ColdFrontWI/Hornet_Cockpit/DXF Files/Panel/Bitmap/Readme.md

# Panel bitmaps

One of the main references when was drawing the panel was the NATOPS instrument panel foldout.  The .png files here
are literal screengrabs from the PDF that I inserted into QCAD and used as a reference for switch spacing.
