ColdFrontWI/Hornet_Cockpit/DXF Files/Panel/Bitmap/AMPCD Full.png

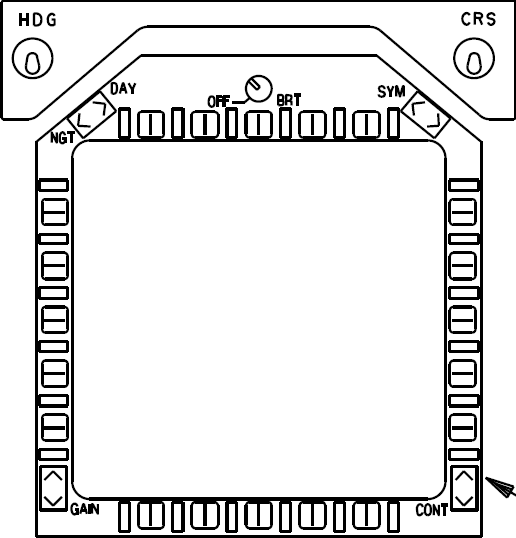
DXF Files/Panel/Bitmap/AMPCD Full.png
