ColdFrontWI/Hornet_Cockpit/DXF Files/Panel/Bitmap/AMPCD Top.png

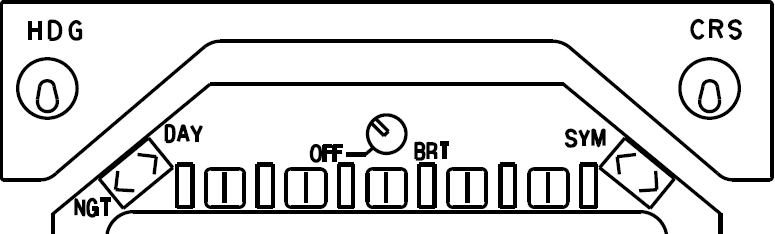
DXF Files/Panel/Bitmap/AMPCD Top.png
