ColdFrontWI/Hornet_Cockpit/DXF Files/Panel/Bitmap/Cons Left Ext Lt.PNG

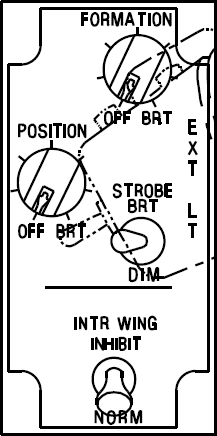
DXF Files/Panel/Bitmap/Cons Left Ext Lt.PNG
