ColdFrontWI/Hornet_Cockpit/DXF Files/Panel/Bitmap/Cons Left Fuel FCS.PNG

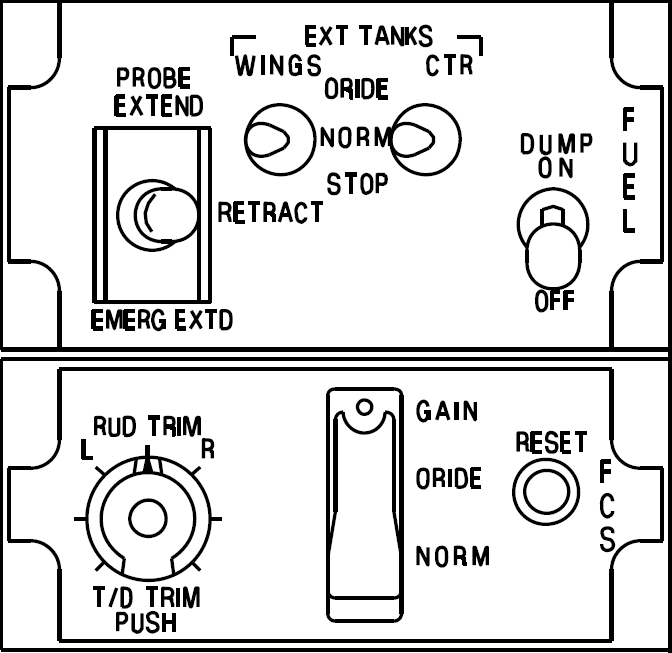
DXF Files/Panel/Bitmap/Cons Left Fuel FCS.PNG
