ColdFrontWI/Hornet_Cockpit/DXF Files/Panel/Bitmap/Cons Left IFF.PNG

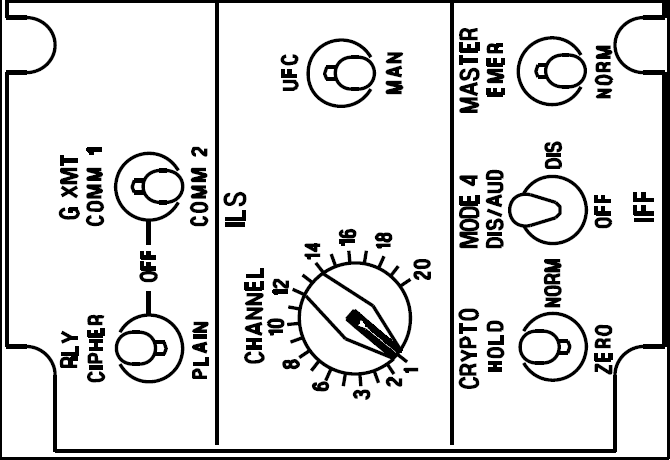
DXF Files/Panel/Bitmap/Cons Left IFF.PNG
