ColdFrontWI/Hornet_Cockpit/DXF Files/Panel/Bitmap/Cons Left OBOGS.PNG

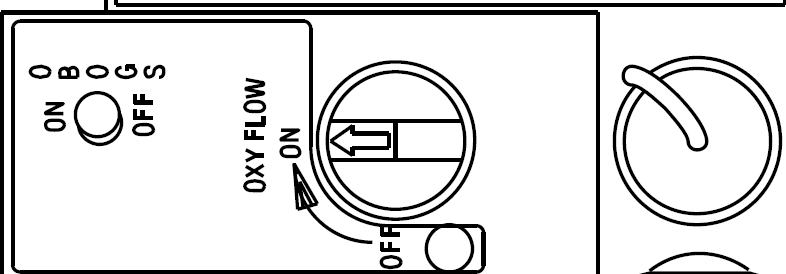
DXF Files/Panel/Bitmap/Cons Left OBOGS.PNG
