ColdFrontWI/Hornet_Cockpit/DXF Files/Panel/Bitmap/Cons Left Vol.PNG

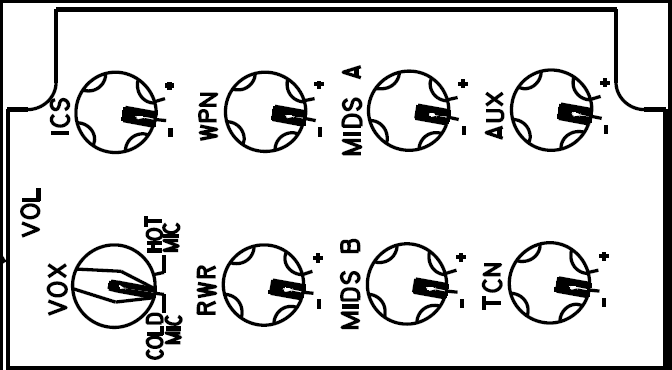
DXF Files/Panel/Bitmap/Cons Left Vol.PNG
