ColdFrontWI/Hornet_Cockpit/DXF Files/Panel/Bitmap/Cons Right Elec.PNG

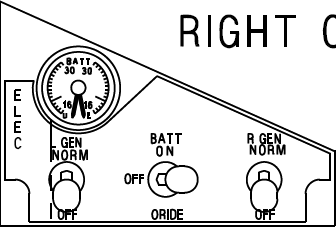
DXF Files/Panel/Bitmap/Cons Right Elec.PNG
