ColdFrontWI/Hornet_Cockpit/DXF Files/Panel/Bitmap/Cons Right ESC.PNG

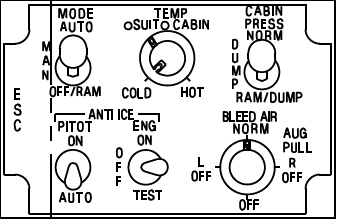
DXF Files/Panel/Bitmap/Cons Right ESC.PNG
