ColdFrontWI/Hornet_Cockpit/DXF Files/Panel/Bitmap/Cons Right Front.PNG

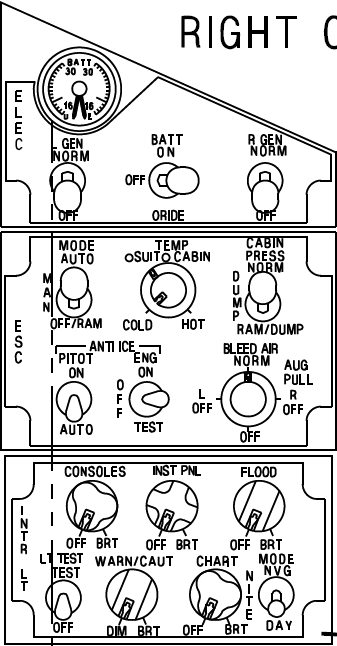
DXF Files/Panel/Bitmap/Cons Right Front.PNG
