ColdFrontWI/Hornet_Cockpit/DXF Files/Panel/Bitmap/Cons Right Int Light.PNG

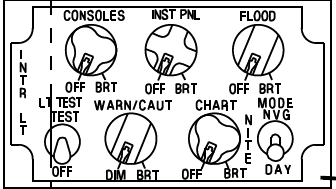
DXF Files/Panel/Bitmap/Cons Right Int Light.PNG
