ColdFrontWI/Hornet_Cockpit/DXF Files/Panel/Bitmap/Cons Right Sensor.PNG

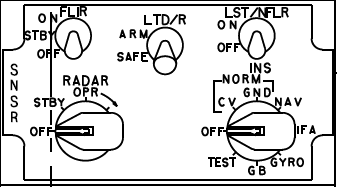
DXF Files/Panel/Bitmap/Cons Right Sensor.PNG
