ColdFrontWI/Hornet_Cockpit/DXF Files/Panel/Bitmap/Flight Inst.PNG

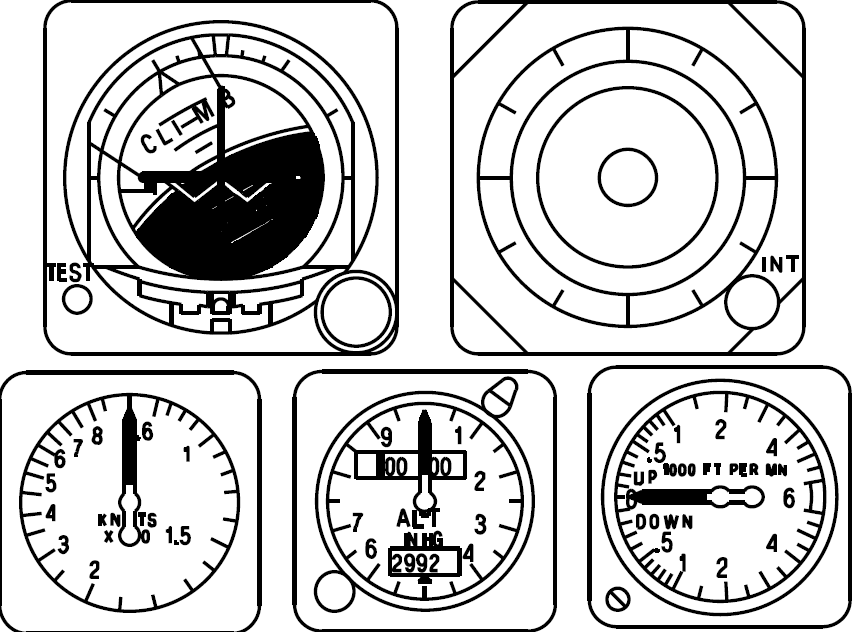
DXF Files/Panel/Bitmap/Flight Inst.PNG
