ColdFrontWI/Hornet_Cockpit/DXF Files/Panel/Bitmap/HMD, Spin Recovery.PNG

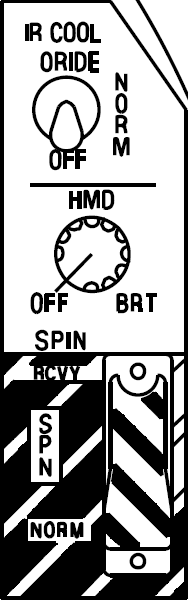
DXF Files/Panel/Bitmap/HMD, Spin Recovery.PNG
