ColdFrontWI/Hornet_Cockpit/DXF Files/Panel/Bitmap/HUD.png

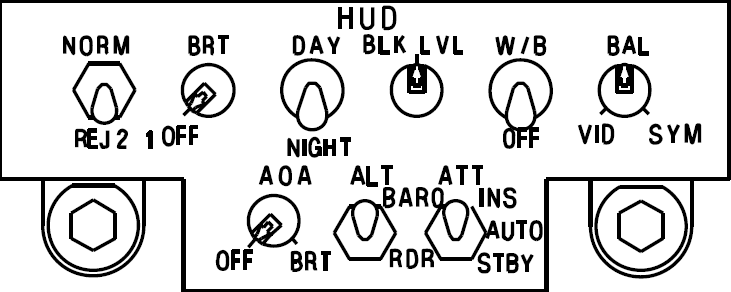
DXF Files/Panel/Bitmap/HUD.png
