ColdFrontWI/Hornet_Cockpit/DXF Files/Panel/Bitmap/Jett Select.PNG

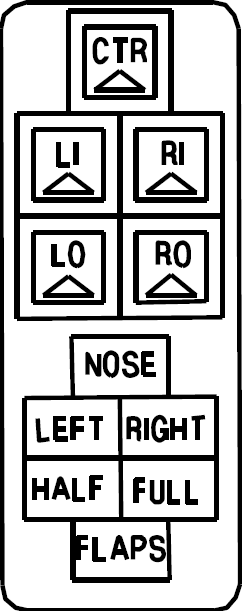
DXF Files/Panel/Bitmap/Jett Select.PNG
