ColdFrontWI/Hornet_Cockpit/DXF Files/Panel/Bitmap/Left Cons APU.PNG

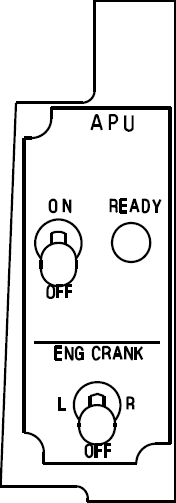
DXF Files/Panel/Bitmap/Left Cons APU.PNG
