ColdFrontWI/Hornet_Cockpit/DXF Files/Panel/Bitmap/Left Cons GndPwr Fire.PNG

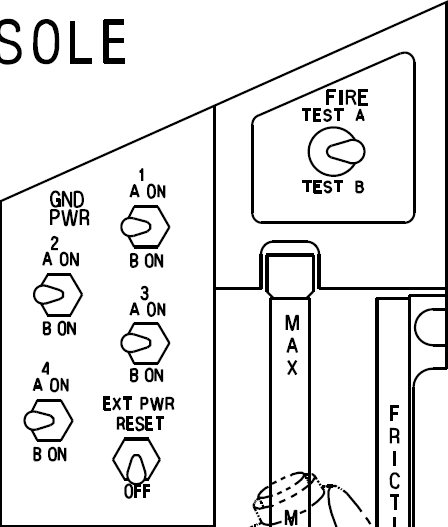
DXF Files/Panel/Bitmap/Left Cons GndPwr Fire.PNG
