ColdFrontWI/Hornet_Cockpit/DXF Files/Panel/Bitmap/Left Mech.PNG

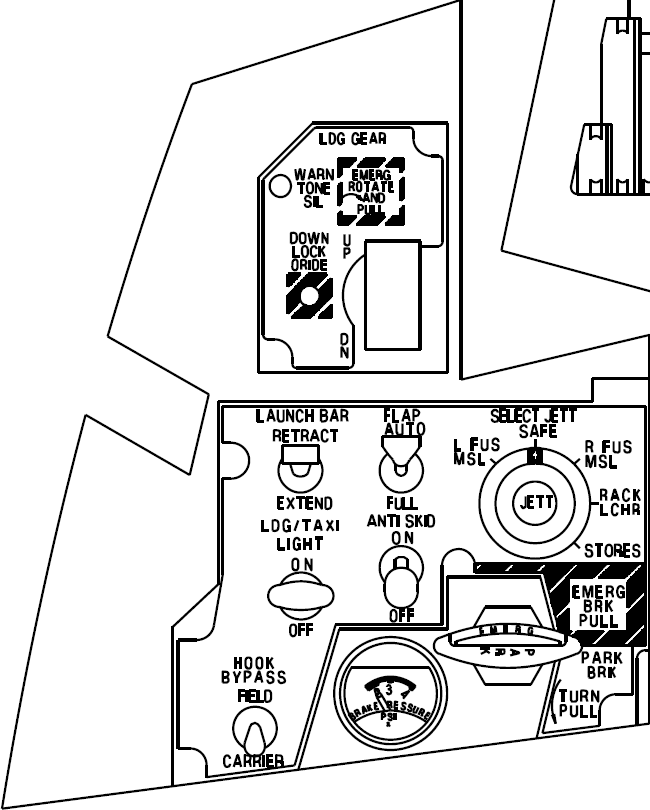
DXF Files/Panel/Bitmap/Left Mech.PNG
