ColdFrontWI/Hornet_Cockpit/DXF Files/Panel/Bitmap/Master Arm.PNG

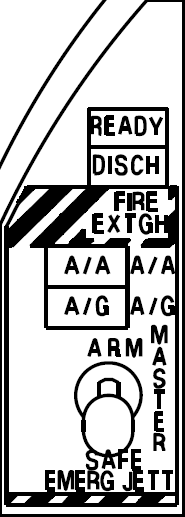
DXF Files/Panel/Bitmap/Master Arm.PNG
