ColdFrontWI/Hornet_Cockpit/DXF Files/Panel/Bitmap/Right Mech.PNG

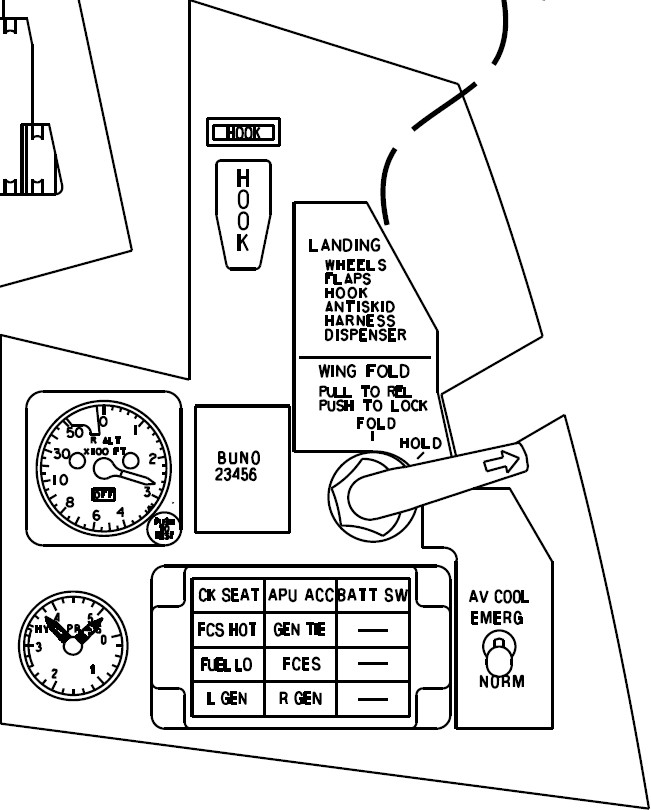
DXF Files/Panel/Bitmap/Right Mech.PNG
