ColdFrontWI/Hornet_Cockpit/DXF Files/Panel/Bitmap/TM Cougar MFD - crop.jpg

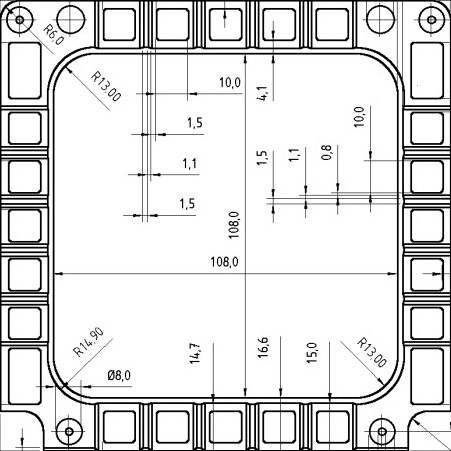
DXF Files/Panel/Bitmap/TM Cougar MFD - crop.jpg
