ColdFrontWI/Hornet_Cockpit/DXF Files/Panel/Bitmap/UFC.png

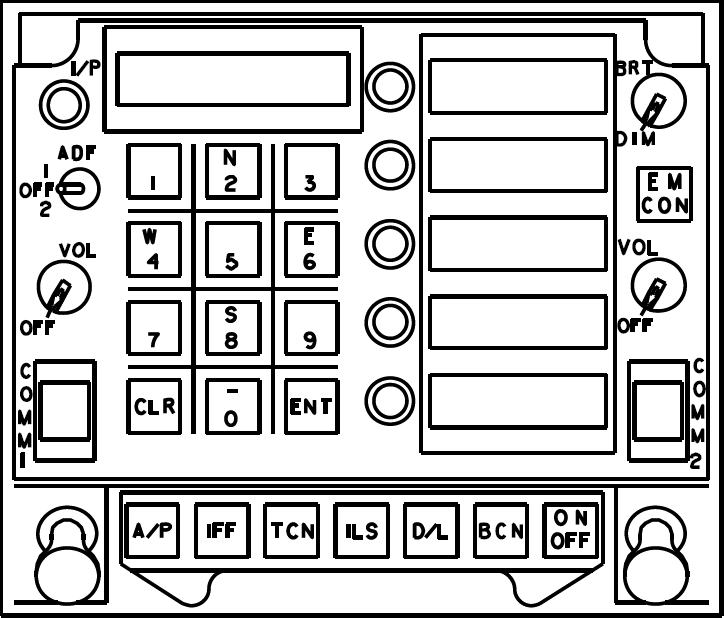
DXF Files/Panel/Bitmap/UFC.png
