ColdFrontWI/Hornet_Cockpit/Pictures/2020-05/IMG_7479.JPG

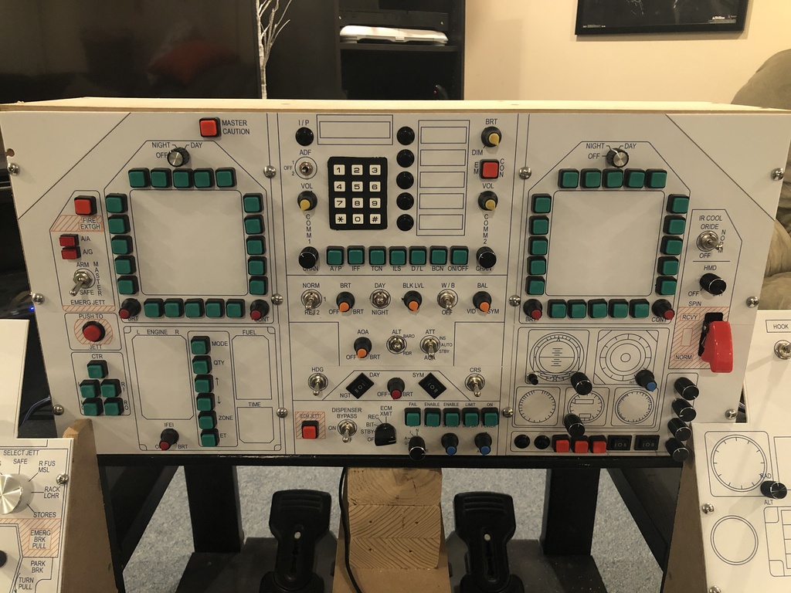
Pictures/2020-05/IMG_7479.JPG
