ColdFrontWI/Hornet_Cockpit/STL Files/Warthog-Virpil extensions/Pictures/IMG_7719.JPG

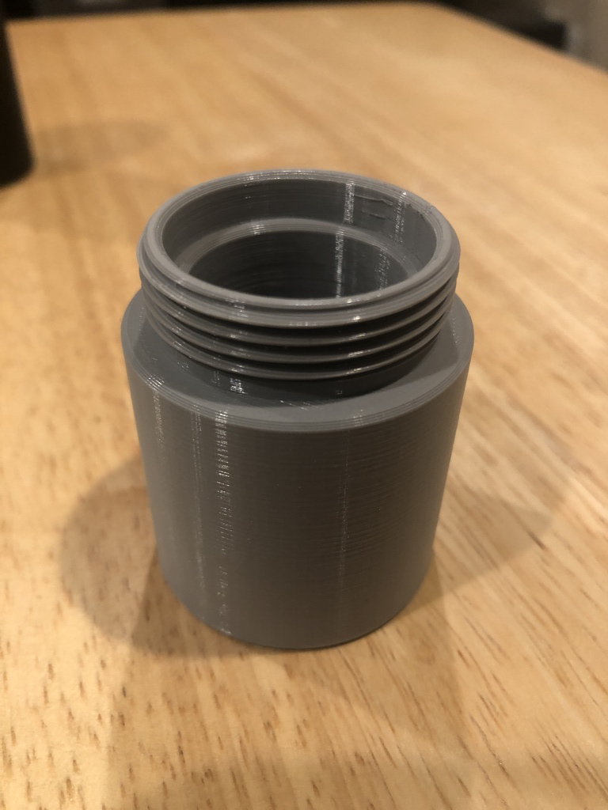
STL Files/Warthog-Virpil extensions/Pictures/IMG_7719.JPG
