ColdFrontWI/Hornet_Cockpit/STL Files/Warthog-Virpil extensions/Pictures/IMG_7722.JPG

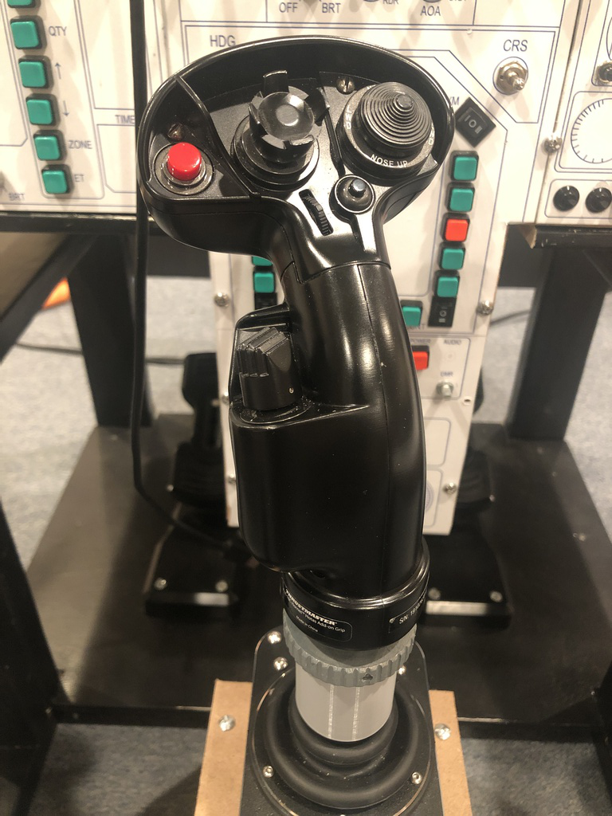
STL Files/Warthog-Virpil extensions/Pictures/IMG_7722.JPG
