ColdFrontWI/Hornet_Cockpit/STL Files/Knobs/Small volume knob.stl

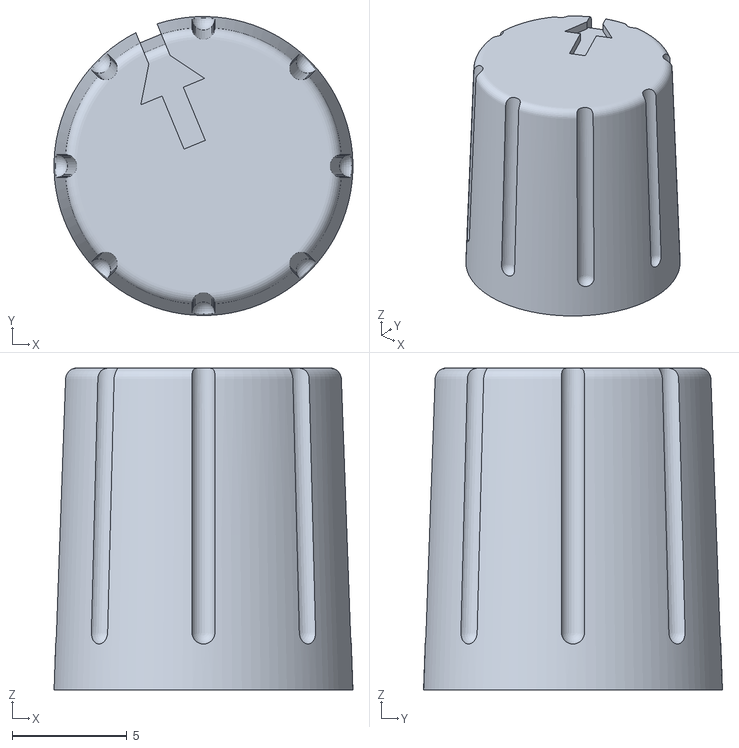
[picture p114: CAD file, 2020-09-19]
STL Files/Knobs/Small volume knob.stl
13.0 x 13.0 x 14.0
