ColdFrontWI/Hornet_Cockpit/STL Files/Other/Hand brake base.stl

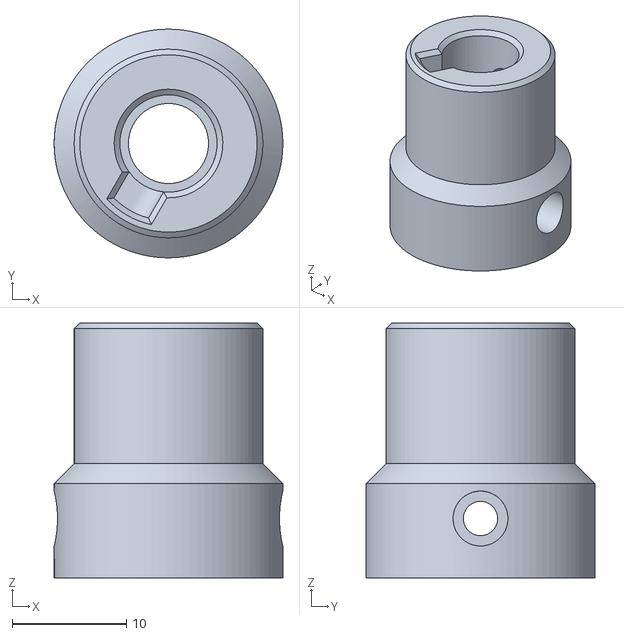
[picture p115: CAD file, 2020-09-13]
STL Files/Other/Hand brake base.stl
20.0 x 20.0 x 22.3
