ColdFrontWI/Hornet_Cockpit/STL Files/Switches/Sw - Landing & taxi lights.stl

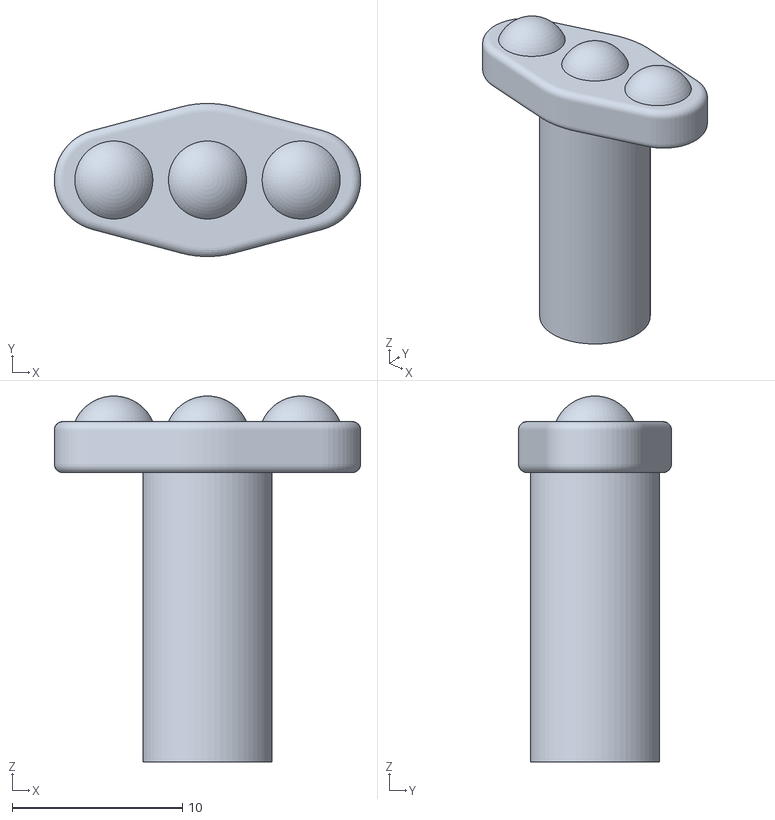
[picture p116: CAD file, 2020-08-24]
STL Files/Switches/Sw - Landing & taxi lights.stl
18.0 x 8.99 x 21.5
