ColdFrontWI/Hornet_Cockpit/STL Files/Warthog-Virpil extensions/WH ext 100mm, 36.5.stl

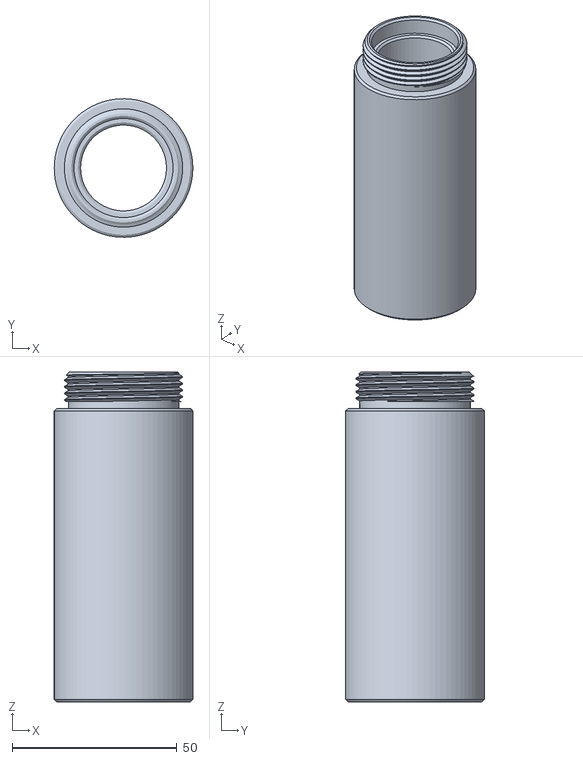
[picture p117: CAD file, 2020-09-23]
STL Files/Warthog-Virpil extensions/WH ext 100mm, 36.5.stl
42.0 x 42.0 x 100.0
