ColdFrontWI/Hornet_Cockpit/STL Files/Knobs/Smaller volume knob.stl

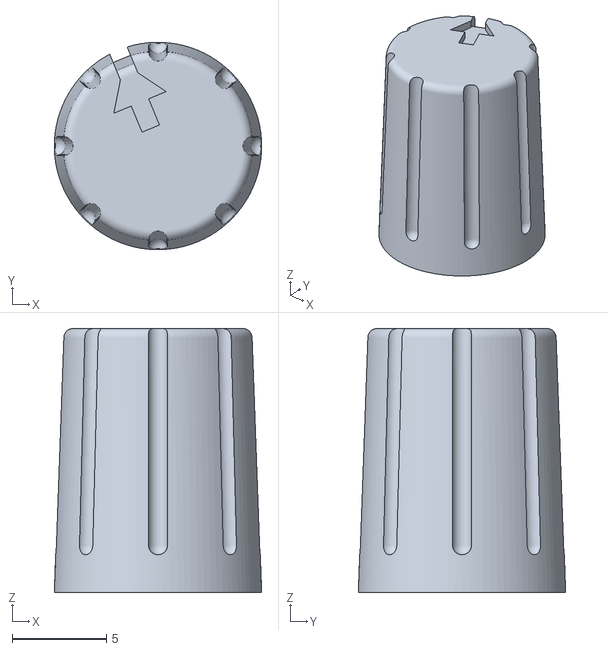
[picture p118: CAD file, 2020-09-19]
STL Files/Knobs/Smaller volume knob.stl
11.0 x 11.0 x 14.0
