ColdFrontWI/Hornet_Cockpit/STL Files/Other/Hand brake shaft.stl

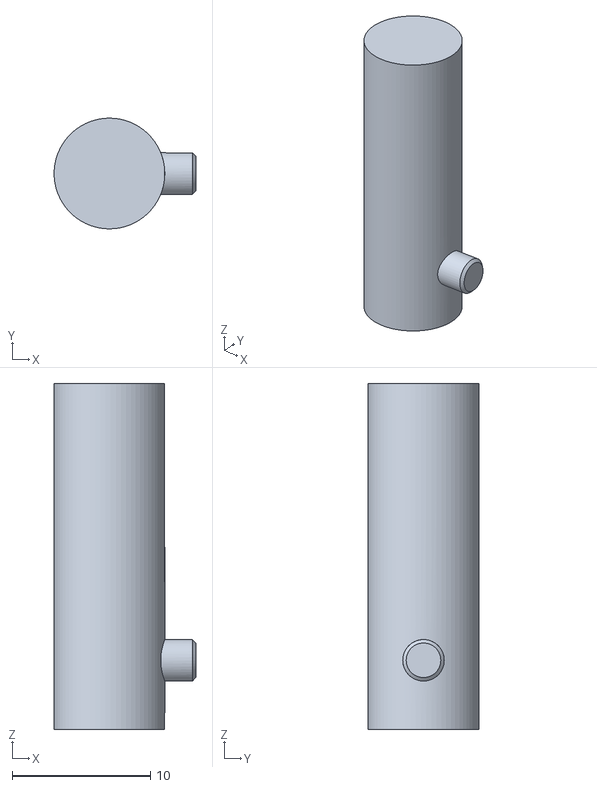
[picture p119: CAD file, 2020-09-13]
STL Files/Other/Hand brake shaft.stl
10.2 x 8.00 x 25.0
