ColdFrontWI/Hornet_Cockpit/STL Files/Switches/Sw - Flat.stl

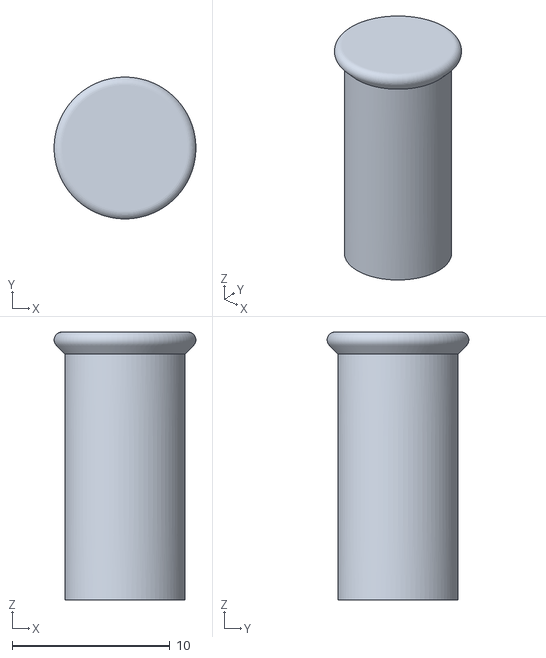
[picture p120: CAD file, 2020-08-24]
STL Files/Switches/Sw - Flat.stl
9.00 x 8.99 x 17.0
