ColdFrontWI/Hornet_Cockpit/STL Files/Knobs/Knob - Large pointy.stl

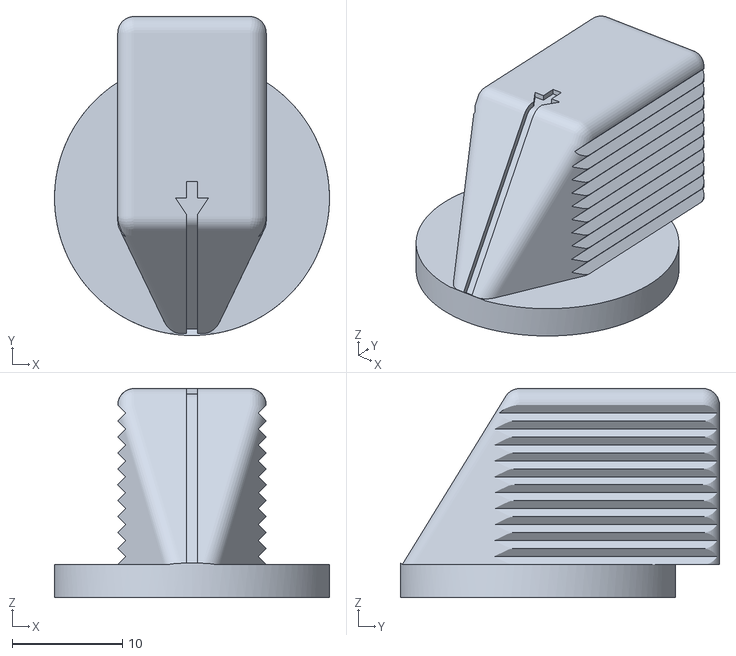
[picture p121: CAD file, 2020-09-13]
STL Files/Knobs/Knob - Large pointy.stl
25.0 x 29.0 x 19.0
