ColdFrontWI/Hornet_Cockpit/STL Files/Other/Dispense button.stl

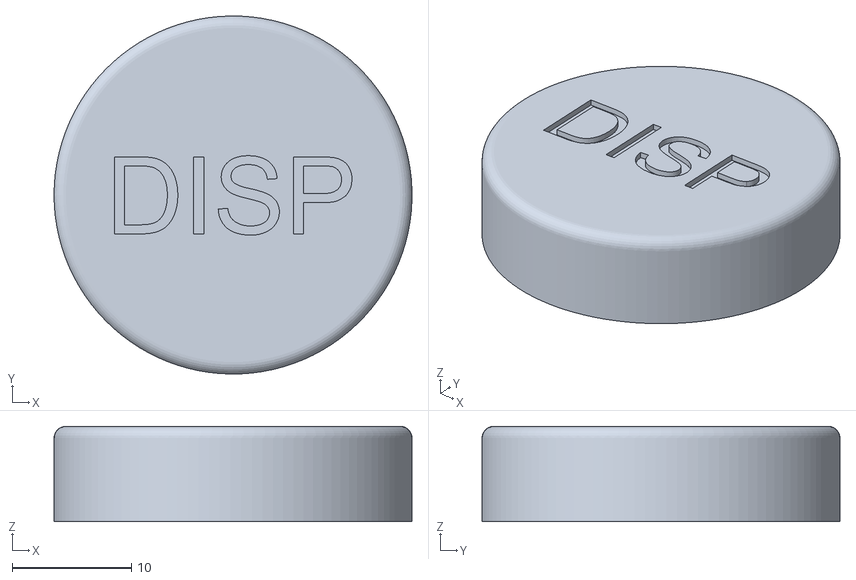
[picture p122: CAD file, 2020-09-13]
STL Files/Other/Dispense button.stl
30.0 x 30.0 x 8.00
