ColdFrontWI/Hornet_Cockpit/STL Files/Switches/Sw - Gear.stl

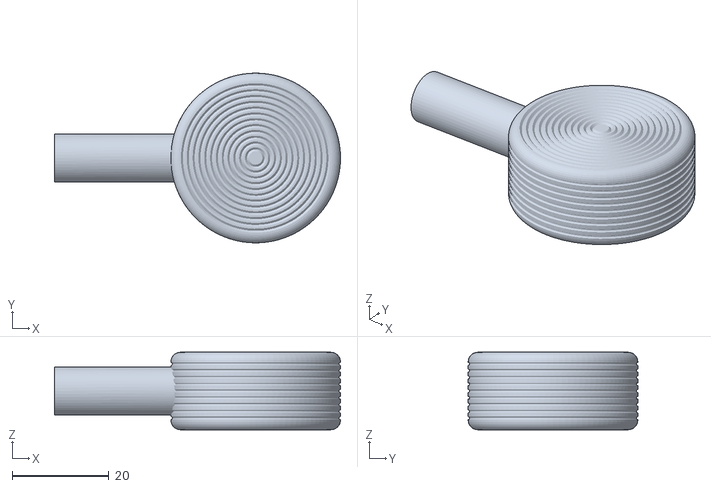
[picture p123: CAD file, 2020-08-24]
STL Files/Switches/Sw - Gear.stl
59.0 x 35.0 x 16.0
