ColdFrontWI/Hornet_Cockpit/STL Files/Knobs/Knob - Bleed air.stl

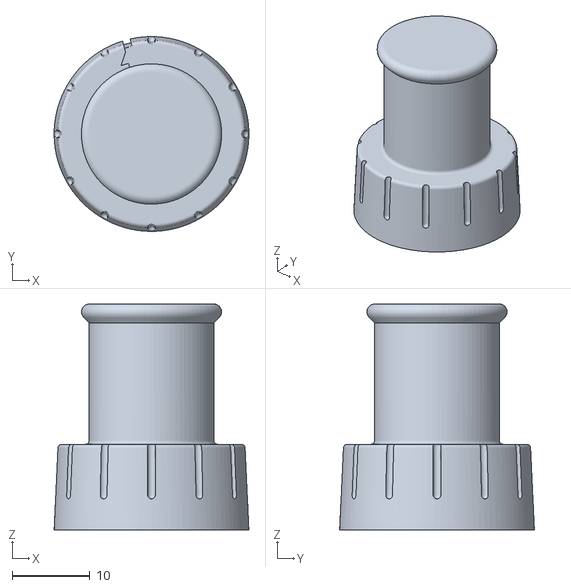
[picture p124: CAD file, 2020-09-05]
STL Files/Knobs/Knob - Bleed air.stl
25.0 x 25.0 x 29.0
