ColdFrontWI/Hornet_Cockpit/STL Files/Other/Hand brake top.stl

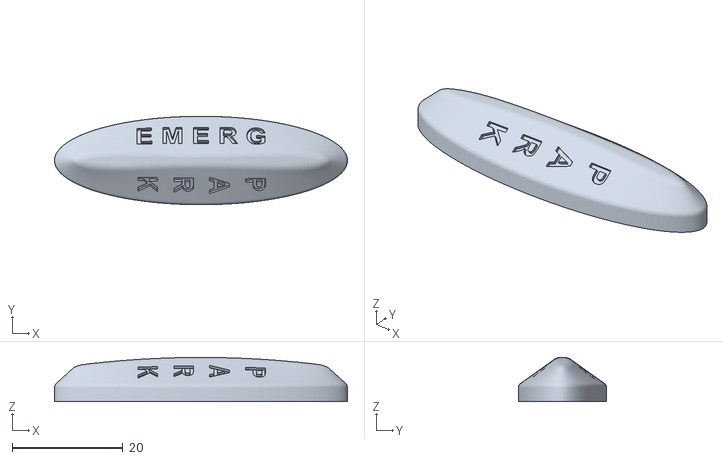
[picture p125: CAD file, 2020-09-13]
STL Files/Other/Hand brake top.stl
53.0 x 16.0 x 8.00
