ColdFrontWI/Hornet_Cockpit/STL Files/Switches/Fuel probe guard.stl

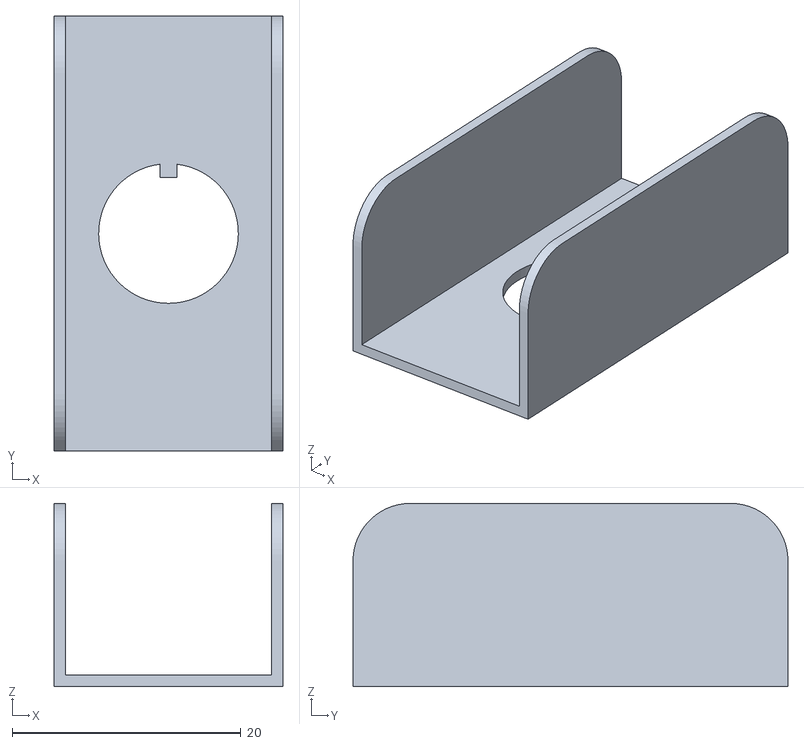
[picture p126: CAD file, 2020-08-24]
STL Files/Switches/Fuel probe guard.stl
20.0 x 38.0 x 16.0
