ColdFrontWI/Hornet_Cockpit/STL Files/Warthog-Virpil extensions/WH ext 25mm, 36.5.stl

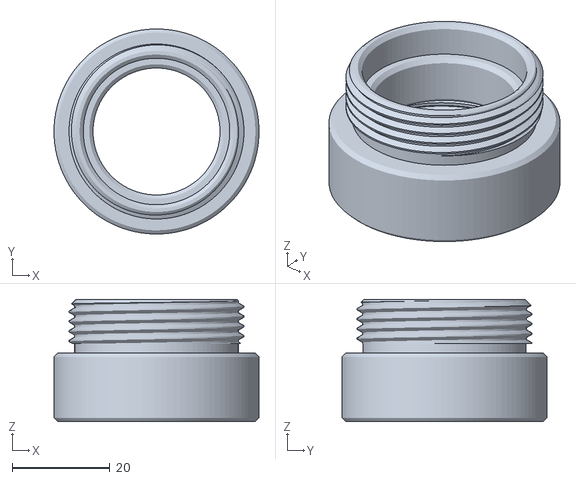
[picture p127: CAD file, 2020-09-23]
STL Files/Warthog-Virpil extensions/WH ext 25mm, 36.5.stl
42.0 x 42.0 x 25.0
