ColdFrontWI/Hornet_Cockpit/STL Files/Knobs/Knob - Suit.stl

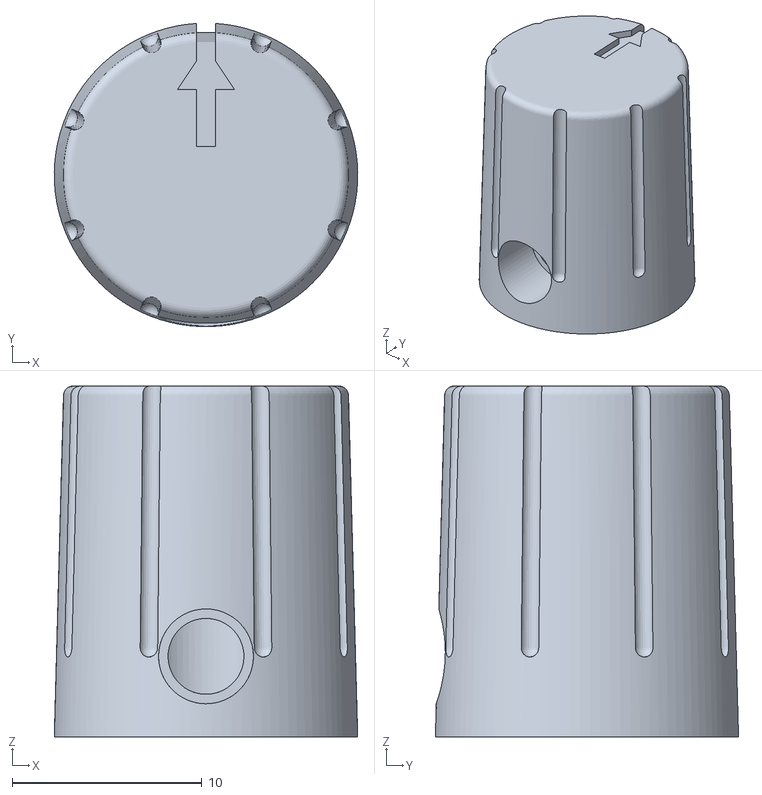
[picture p128: CAD file, 2020-09-05]
STL Files/Knobs/Knob - Suit.stl
16.0 x 16.0 x 18.5
