ColdFrontWI/Hornet_Cockpit/STL Files/Other/Button adapter.stl

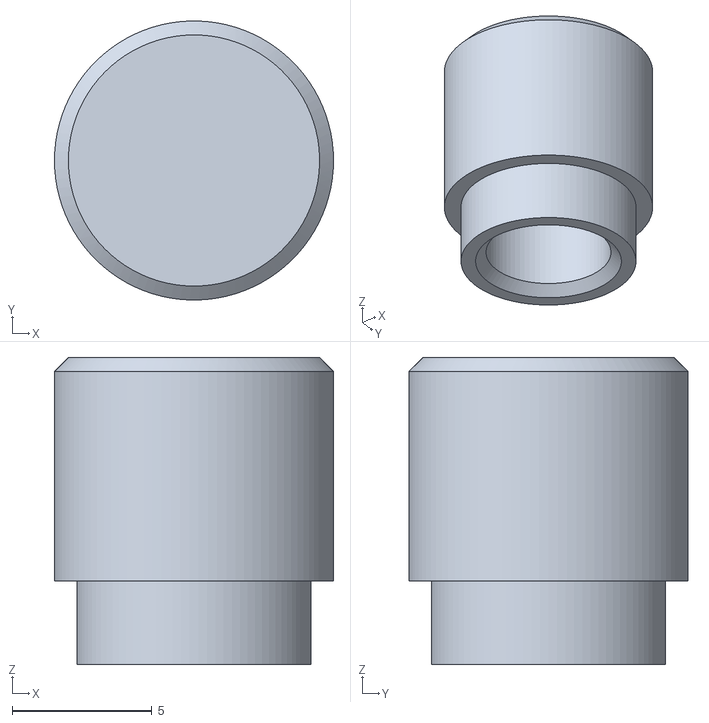
[picture p129: CAD file, 2020-08-30]
STL Files/Other/Button adapter.stl
10.0 x 9.99 x 11.0
