ColdFrontWI/Hornet_Cockpit/STL Files/Switches/Sw - Flaps.stl

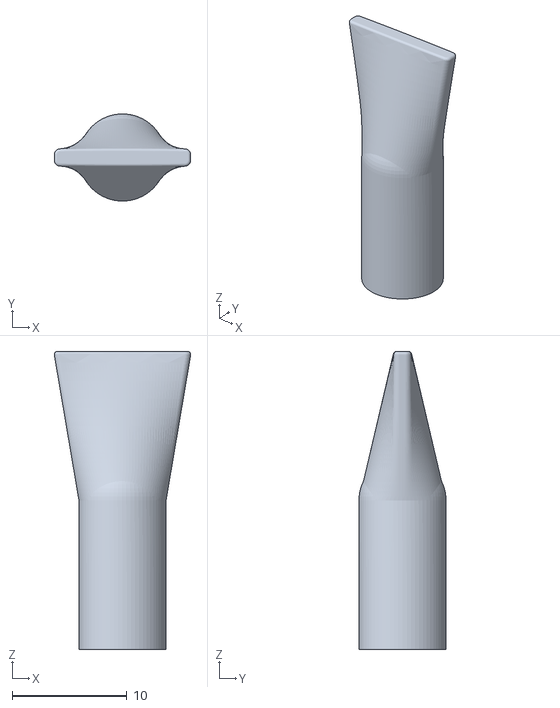
[picture p130: CAD file, 2020-08-24]
STL Files/Switches/Sw - Flaps.stl
11.9 x 7.60 x 26.0
