ColdFrontWI/Hornet_Cockpit/STL Files/Knobs/Knob - Cabin.stl

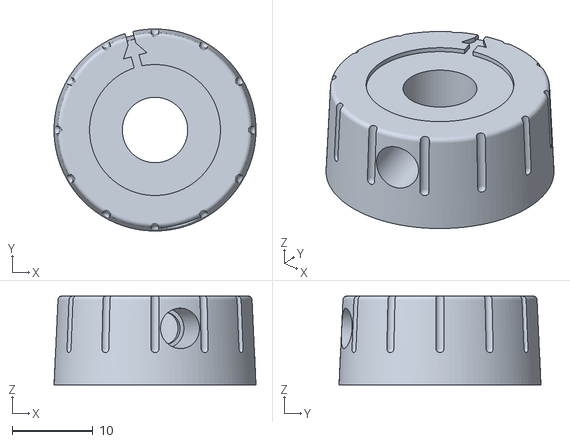
[picture p131: CAD file, 2020-09-05]
STL Files/Knobs/Knob - Cabin.stl
25.0 x 25.0 x 11.0
