ColdFrontWI/Hornet_Cockpit/STL Files/Other/Multiselector gear 18t.stl

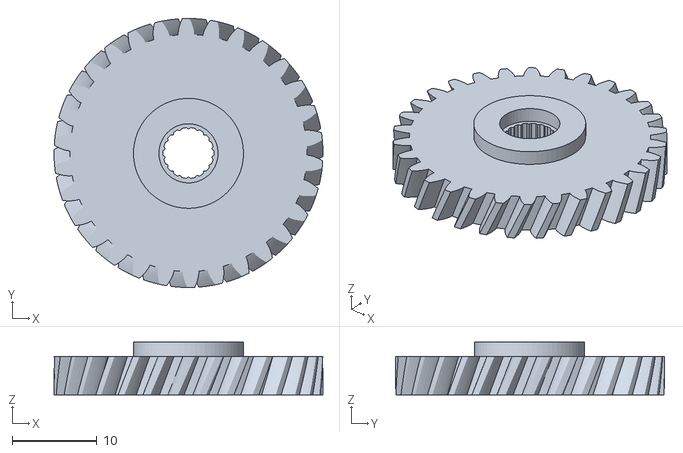
[picture p132: CAD file, 2020-08-30]
STL Files/Other/Multiselector gear 18t.stl
31.8 x 31.8 x 6.20
