ColdFrontWI/Hornet_Cockpit/STL Files/Switches/Sw - Hook.stl

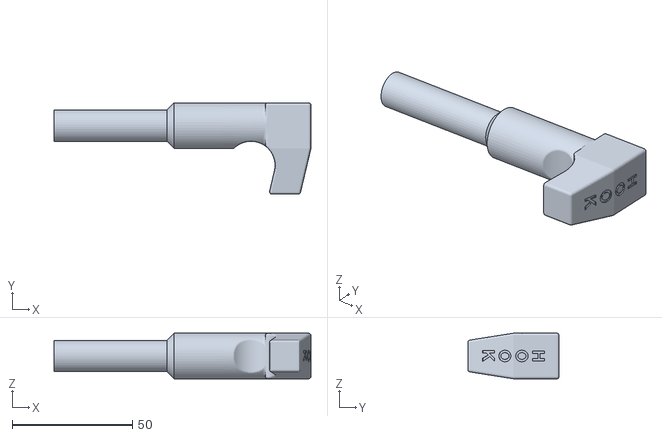
[picture p133: CAD file, 2020-08-24]
STL Files/Switches/Sw - Hook.stl
107.0 x 38.0 x 19.0
