ColdFrontWI/Hornet_Cockpit/STL Files/Warthog-Virpil extensions/WH ext 25mm, 36.0.stl

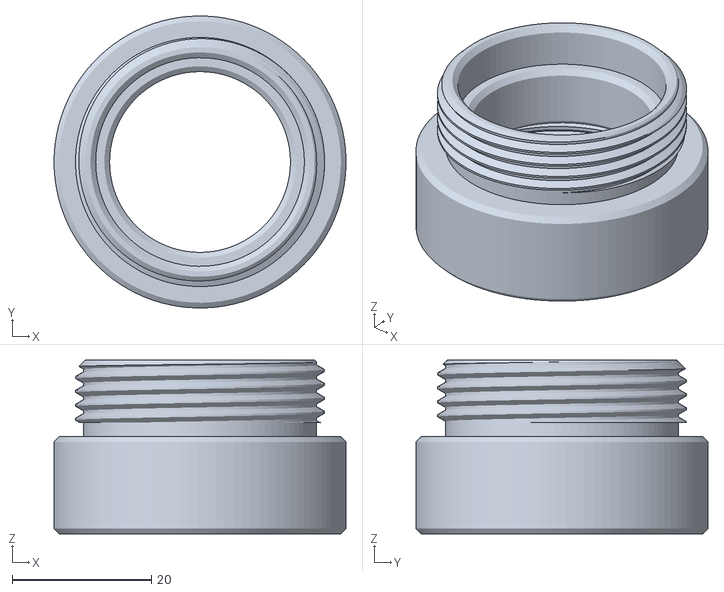
[picture p134: CAD file, 2020-09-20]
STL Files/Warthog-Virpil extensions/WH ext 25mm, 36.0.stl
42.0 x 42.0 x 25.0
