ColdFrontWI/Hornet_Cockpit/STL Files/Knobs/Knob - Rudder trim.stl

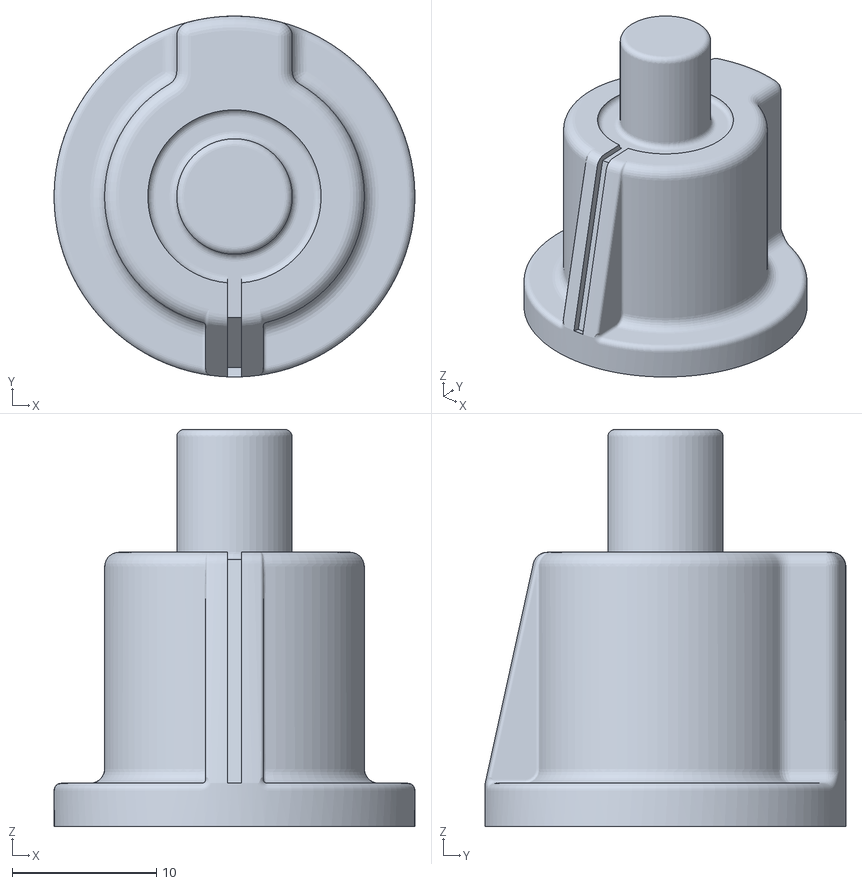
[picture p135: CAD file, 2020-09-04]
STL Files/Knobs/Knob - Rudder trim.stl
25.0 x 25.0 x 27.5
