ColdFrontWI/Hornet_Cockpit/STL Files/Other/Panel - lower LG.stl

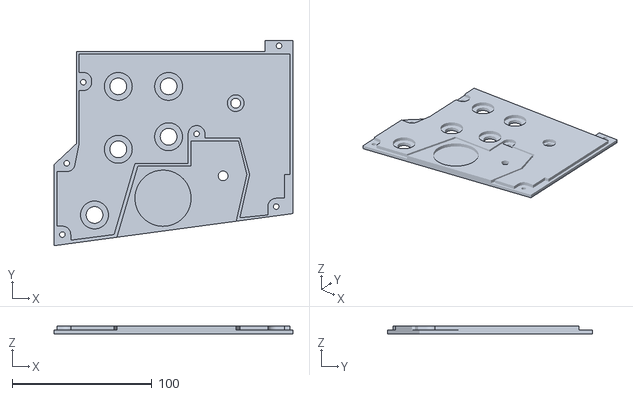
[picture p136: CAD file, 2020-08-30]
STL Files/Other/Panel - lower LG.stl
171.0 x 147.0 x 6.00
