ColdFrontWI/Hornet_Cockpit/STL Files/Knobs/Knob - Large pointy, D-shaft short.stl

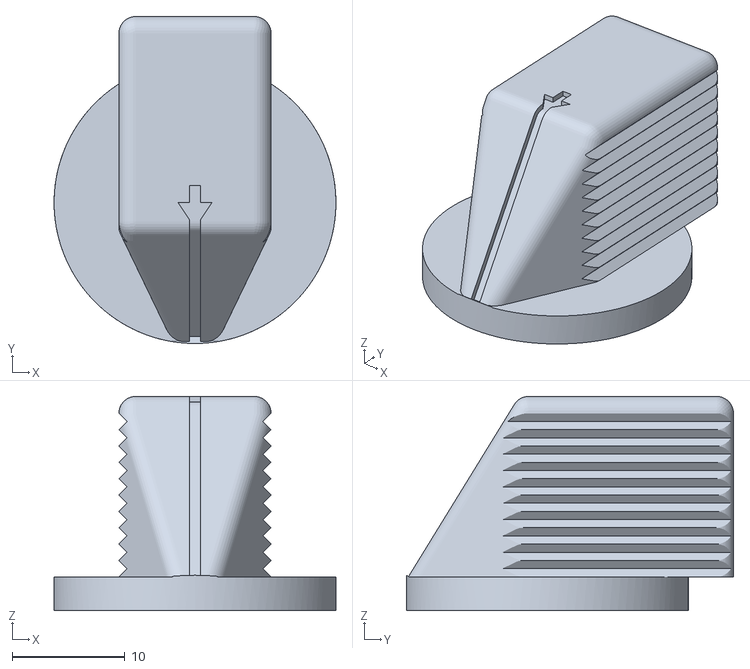
[picture p137: CAD file, 2020-08-31]
STL Files/Knobs/Knob - Large pointy, D-shaft short.stl
25.0 x 29.0 x 19.0
