ColdFrontWI/Hornet_Cockpit/STL Files/Knobs/Knob - Radio tune.stl

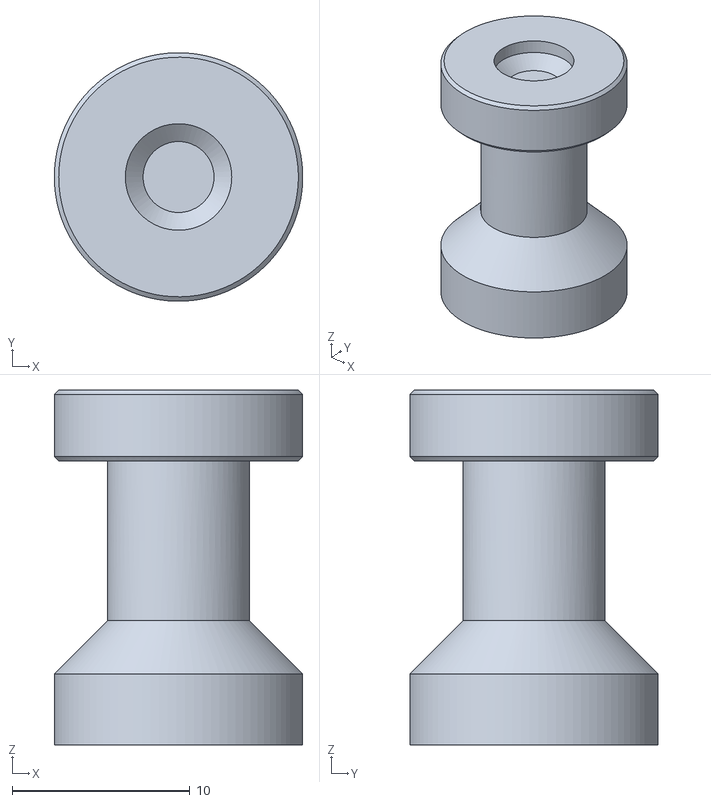
[picture p139: CAD file, 2020-08-24]
STL Files/Knobs/Knob - Radio tune.stl
14.0 x 14.0 x 20.0
