ColdFrontWI/Hornet_Cockpit/STL Files/Knobs/Knob - Small double point.stl

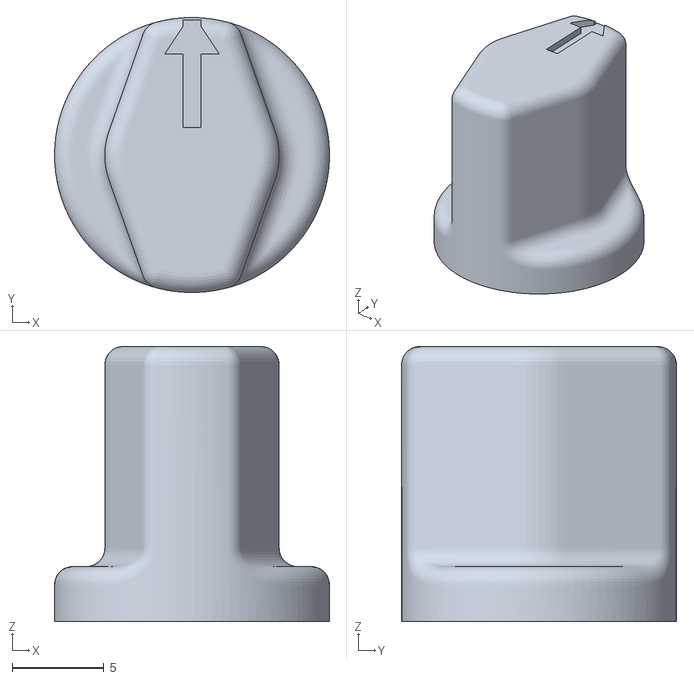
[picture p140: CAD file, 2020-08-24]
STL Files/Knobs/Knob - Small double point.stl
15.0 x 15.0 x 15.0
