ColdFrontWI/Hornet_Cockpit/STL Files/Knobs/Knob - Flat sides.stl

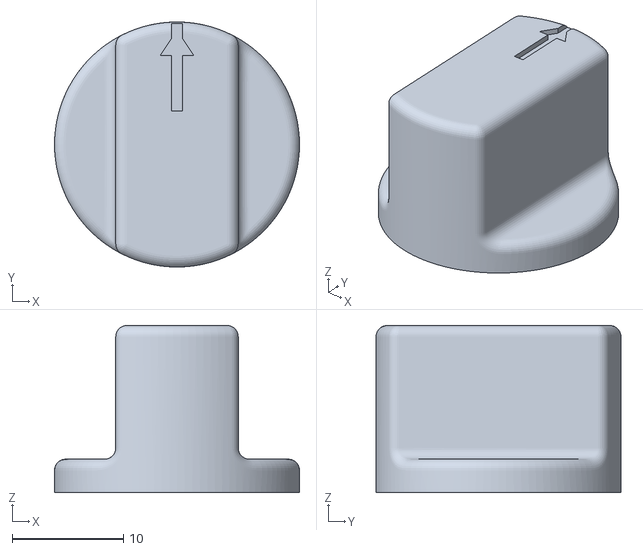
[picture p141: CAD file, 2020-08-24]
STL Files/Knobs/Knob - Flat sides.stl
22.0 x 22.0 x 15.0
