ColdFrontWI/Hornet_Cockpit/STL Files/Knobs/Knob - Quad.stl

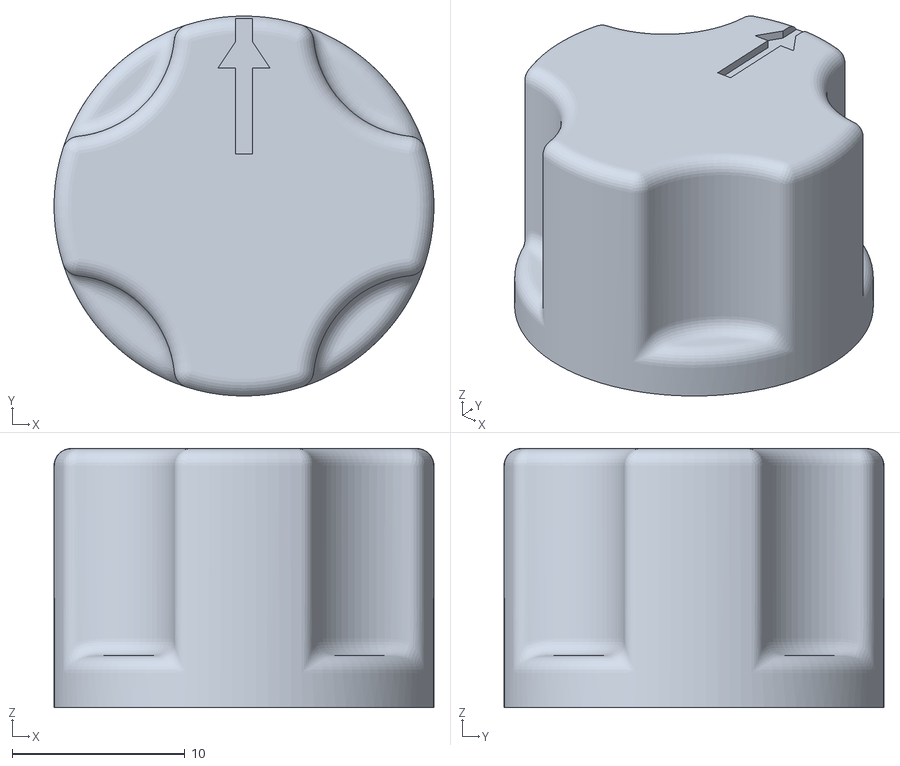
[picture p142: CAD file, 2020-08-24]
STL Files/Knobs/Knob - Quad.stl
22.0 x 22.0 x 15.0
