ColdFrontWI/Hornet_Cockpit/STL Files/Knobs/Knob - Parking brake.stl

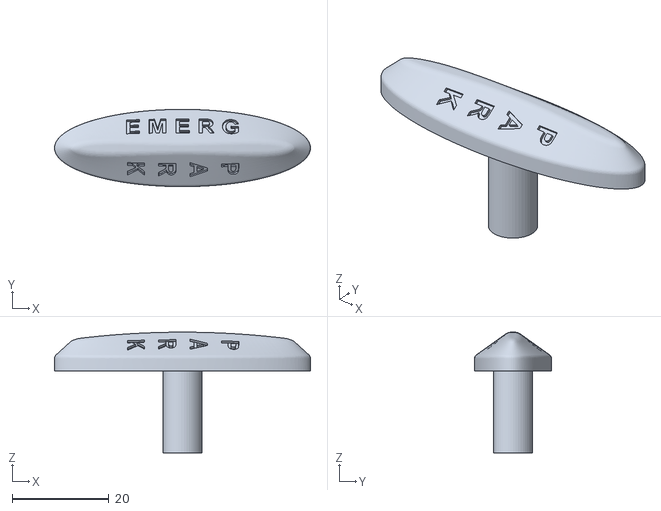
[picture p143: CAD file, 2020-08-24]
STL Files/Knobs/Knob - Parking brake.stl
53.0 x 16.0 x 25.0
