ColdFrontWI/Hornet_Cockpit/STL Files/Knobs/Knob - Triple.stl

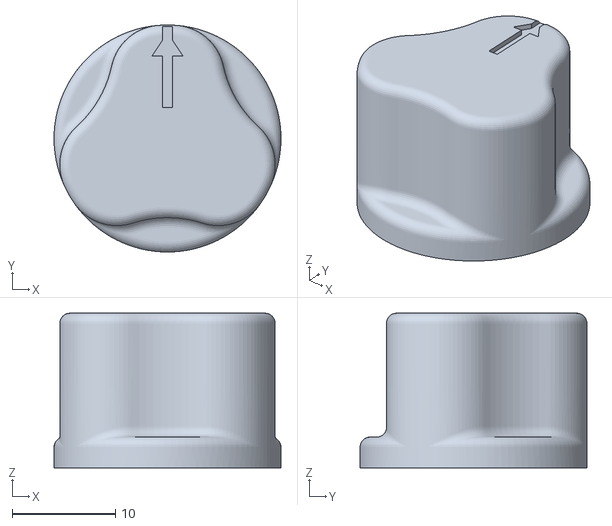
[picture p144: CAD file, 2020-08-24]
STL Files/Knobs/Knob - Triple.stl
22.0 x 22.0 x 15.0
